kocurel/TCGLifeCounterESP32/main/console_init.c

#include "argtable3/argtable3.h"
#include "driver/uart.h"
#include "driver/usb_serial_jtag.h"
#include "esp_console.h"
#include "esp_log.h"
#include "esp_system.h"
#include "esp_vfs_dev.h"
#include "esp_vfs_usb_serial_jtag.h"
#include "freertos/FreeRTOS.h"
#include "linenoise/linenoise.h"
#include "sdkconfig.h"
#include "soc/soc_caps.h"

void initialize_console() {
    /* Drain stdout before reconfiguring it */
    fflush(stdout);
    fsync(fileno(stdout));

    /* Disable buffering on stdin */
    setvbuf(stdin, NULL, _IONBF, 0);

    /* Minicom, screen, idf_monitor send CR when ENTER key is pressed */
    esp_vfs_dev_usb_serial_jtag_set_rx_line_endings(ESP_LINE_ENDINGS_CR);

    /* Move the caret to the beginning of the next line on '\n' */
    esp_vfs_dev_usb_serial_jtag_set_tx_line_endings(ESP_LINE_ENDINGS_CRLF);

    /* Install USB-SERIAL-JTAG driver for interrupt-driven reads and writes
     */
    usb_serial_jtag_driver_config_t usb_serial_jtag_config = {
        .tx_buffer_size = 256,
        .rx_buffer_size = 256,
    };
    ESP_ERROR_CHECK(usb_serial_jtag_driver_install(&usb_serial_jtag_config));

    /* Tell VFS to use USB-SERIAL-JTAG driver */
    esp_vfs_usb_serial_jtag_use_driver();

    /* Initialize the console */
    esp_console_config_t console_config = {.max_cmdline_args = 8,
                                           .max_cmdline_length = 256,
#if CONFIG_LOG_COLORS
                                           .hint_color = atoi(LOG_COLOR_CYAN)
#endif
    };
    ESP_ERROR_CHECK(esp_console_init(&console_config));

    /* Configure linenoise line completion library */
    linenoiseSetMultiLine(1);
    linenoiseSetCompletionCallback(&esp_console_get_completion);
    linenoiseSetHintsCallback((linenoiseHintsCallback*)&esp_console_get_hint);
    linenoiseHistorySetMaxLen(100);
    linenoiseSetMaxLineLen(console_config.max_cmdline_length);
    linenoiseAllowEmpty(false);
}

#include "freertos/FreeRTOS.h"
#include "freertos/task.h"

void console_task(void* pvParameters) {
    // 1. Initialize (The first half of your code)
    initialize_console();
    esp_console_register_help_command();
    // register_system_common();
    // ViewController_register_button_commands();
    // register_system_sleep();

    const char* prompt = LOG_COLOR_I "> " LOG_RESET_COLOR;

    // 2. The Loop
    while (true) {
        char* line = linenoise(prompt);
        if (line == NULL) {
            break;
        }

        if (strlen(line) > 0) {
            linenoiseHistoryAdd(line);
        }

        /* Try to run the command */
        int ret;
        esp_err_t err = esp_console_run(line, &ret);
        if (err == ESP_ERR_NOT_FOUND) {
            printf("Unrecognized command\n");
        } else if (err == ESP_ERR_INVALID_ARG) {
            // command was empty
        } else if (err == ESP_OK && ret != ESP_OK) {
            printf("Command returned non-zero error code: 0x%x (%s)\n", ret,
                   esp_err_to_name(ret));
        } else if (err != ESP_OK) {
            printf("Internal error: %s\n", esp_err_to_name(err));
        }
        /* linenoise allocates line buffer on the heap, so need to free it */
        linenoiseFree(line);
    }

    // 3. Cleanup
    esp_console_deinit();
    vTaskDelete(NULL);  // Tasks must always delete themselves before exiting!
}
